jdesnoyers/Mixed-Reality-MIDI-Keyboard/20170806_183646.jpg

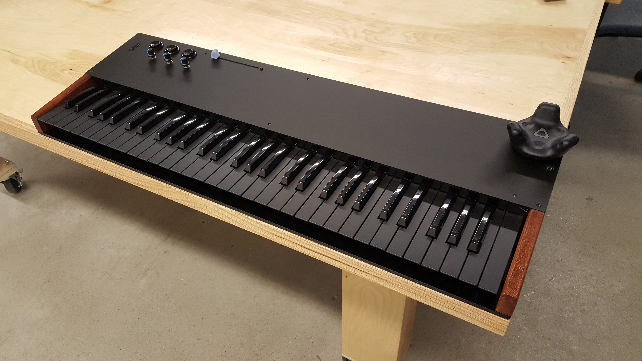
20170806_183646.jpg
