jdesnoyers/Mixed-Reality-MIDI-Keyboard/Unity/VR Interactive Keyboard 3/Assets/Models/UV Maps/IMG_1047.jpg

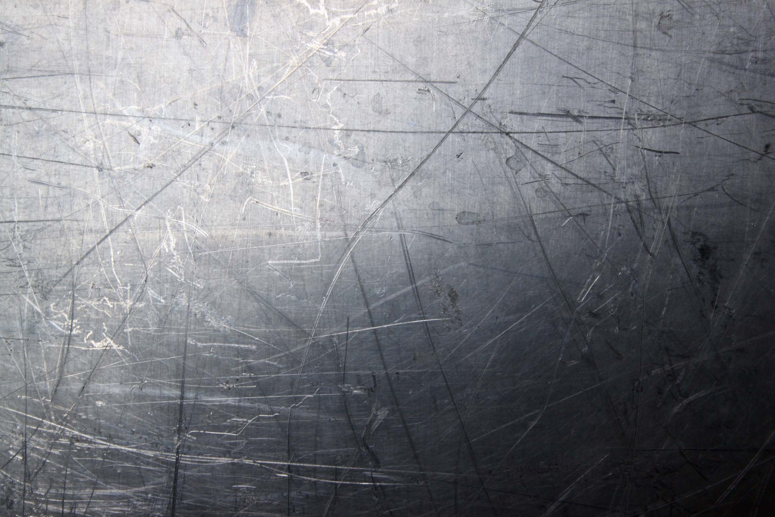
Unity/VR Interactive Keyboard 3/Assets/Models/UV Maps/IMG_1047.jpg
