jdesnoyers/Mixed-Reality-MIDI-Keyboard/Unity/VR Interactive Keyboard 3/Assets/Models/UV Maps/MR MIDI Keyboard - Metal Pieces.png

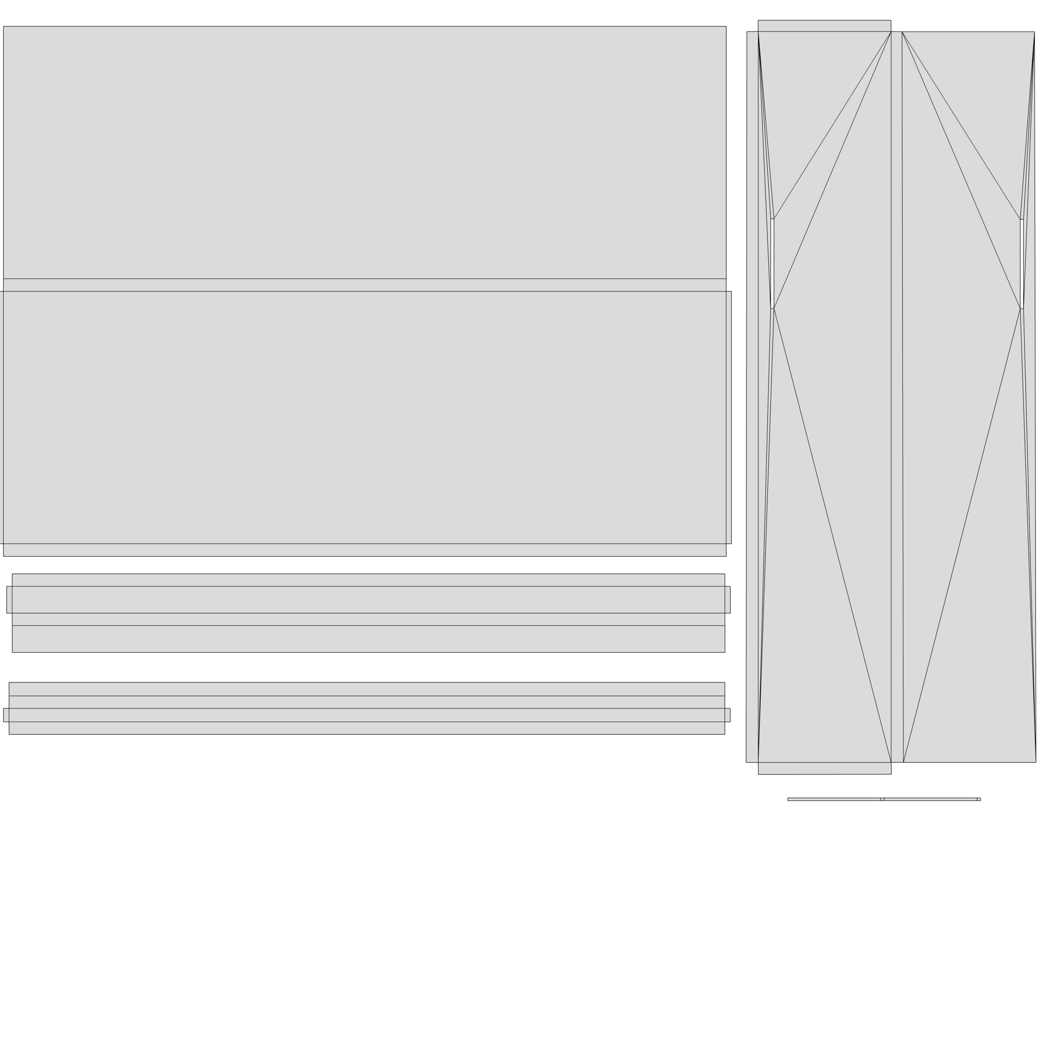
Unity/VR Interactive Keyboard 3/Assets/Models/UV Maps/MR MIDI Keyboard - Metal Pieces.png
