jdesnoyers/Mixed-Reality-MIDI-Keyboard/Unity/VR Interactive Keyboard 3/Assets/Models/UV Maps/texturegen_2057.jpg

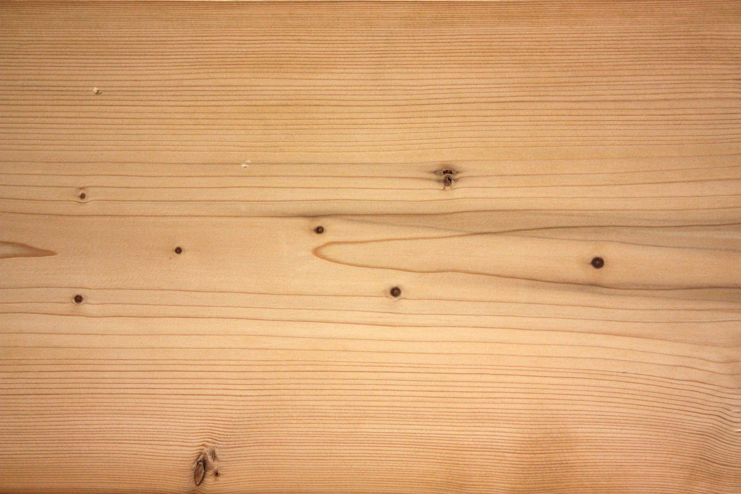
Unity/VR Interactive Keyboard 3/Assets/Models/UV Maps/texturegen_2057.jpg
