jdesnoyers/Mixed-Reality-MIDI-Keyboard/Unity/VR Interactive Keyboard 3/Assets/Models/UV Maps/texturegen_2759.jpg

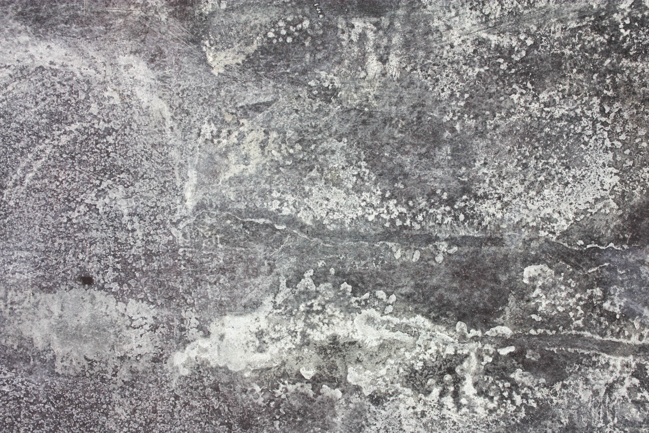
Unity/VR Interactive Keyboard 3/Assets/Models/UV Maps/texturegen_2759.jpg
