jdesnoyers/Mixed-Reality-MIDI-Keyboard/Unity/VR Interactive Keyboard 3/Assets/Models/UV Maps/texturegen__0848.jpg

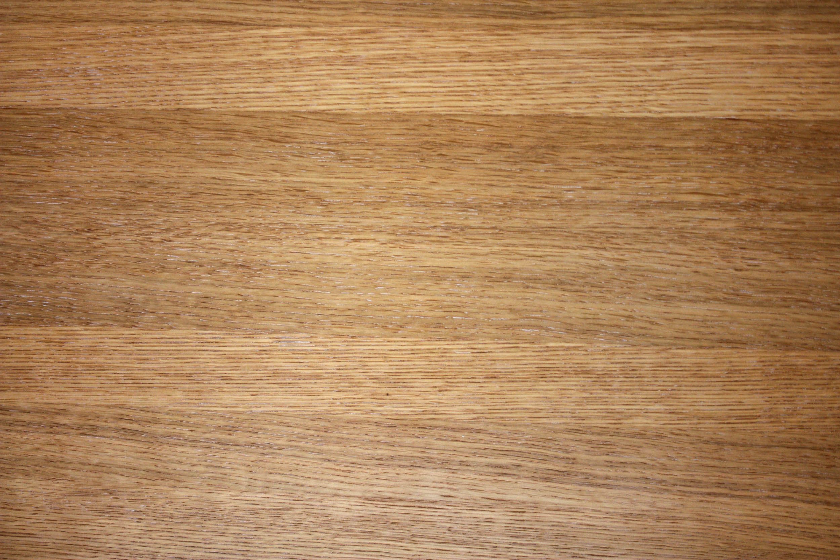
Unity/VR Interactive Keyboard 3/Assets/Models/UV Maps/texturegen__0848.jpg
