jdesnoyers/Mixed-Reality-MIDI-Keyboard/Unity/VR Interactive Keyboard 3/Assets/Models/UV Maps/Wood-2756.jpg

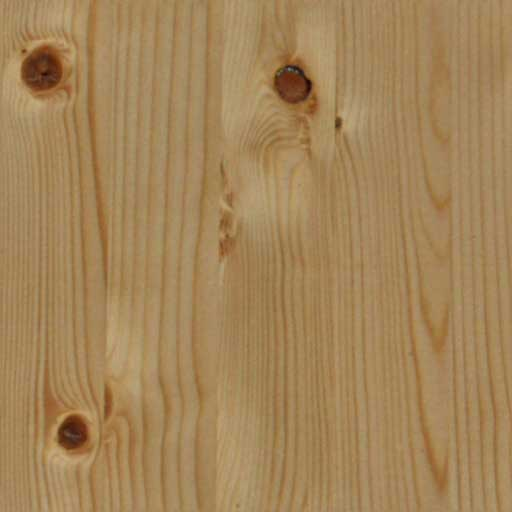
Unity/VR Interactive Keyboard 3/Assets/Models/UV Maps/Wood-2756.jpg
